JerinTJ-7/esp32-8x16-led-matrix-display/Images/led display pcb5.png

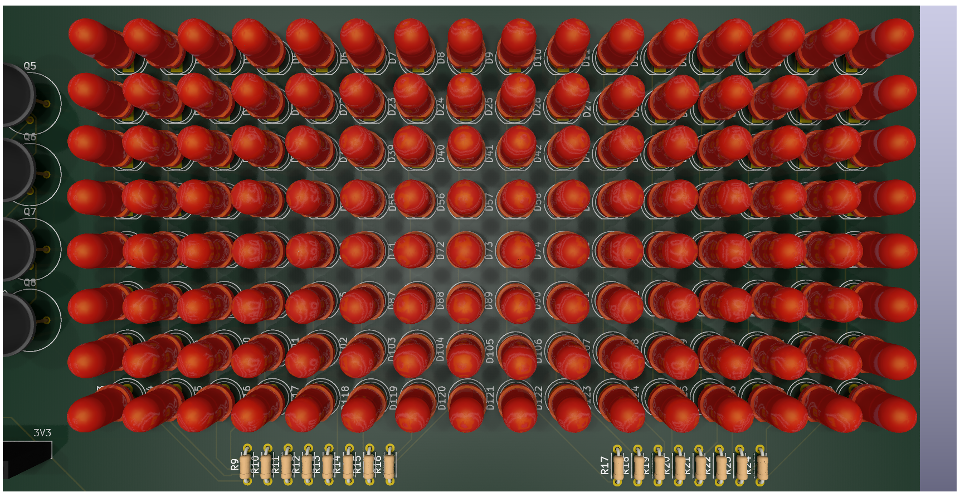
Images/led display pcb5.png
