JerinTJ-7/esp32-8x16-led-matrix-display/Images/led display pcb7.png

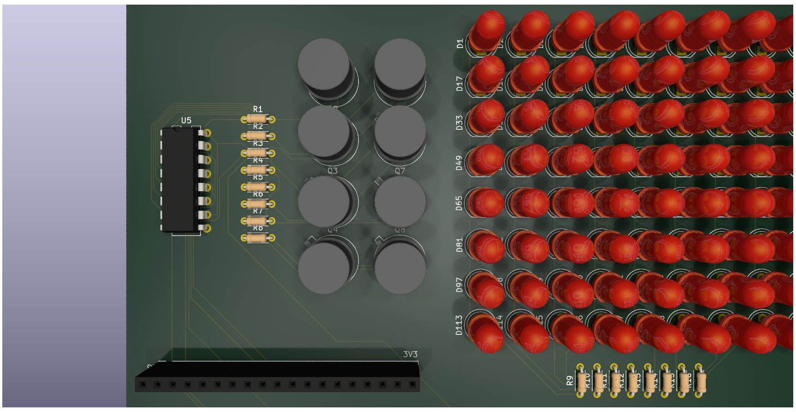
Images/led display pcb7.png
