JerinTJ-7/esp32-8x16-led-matrix-display/Images/PCB Layout.png

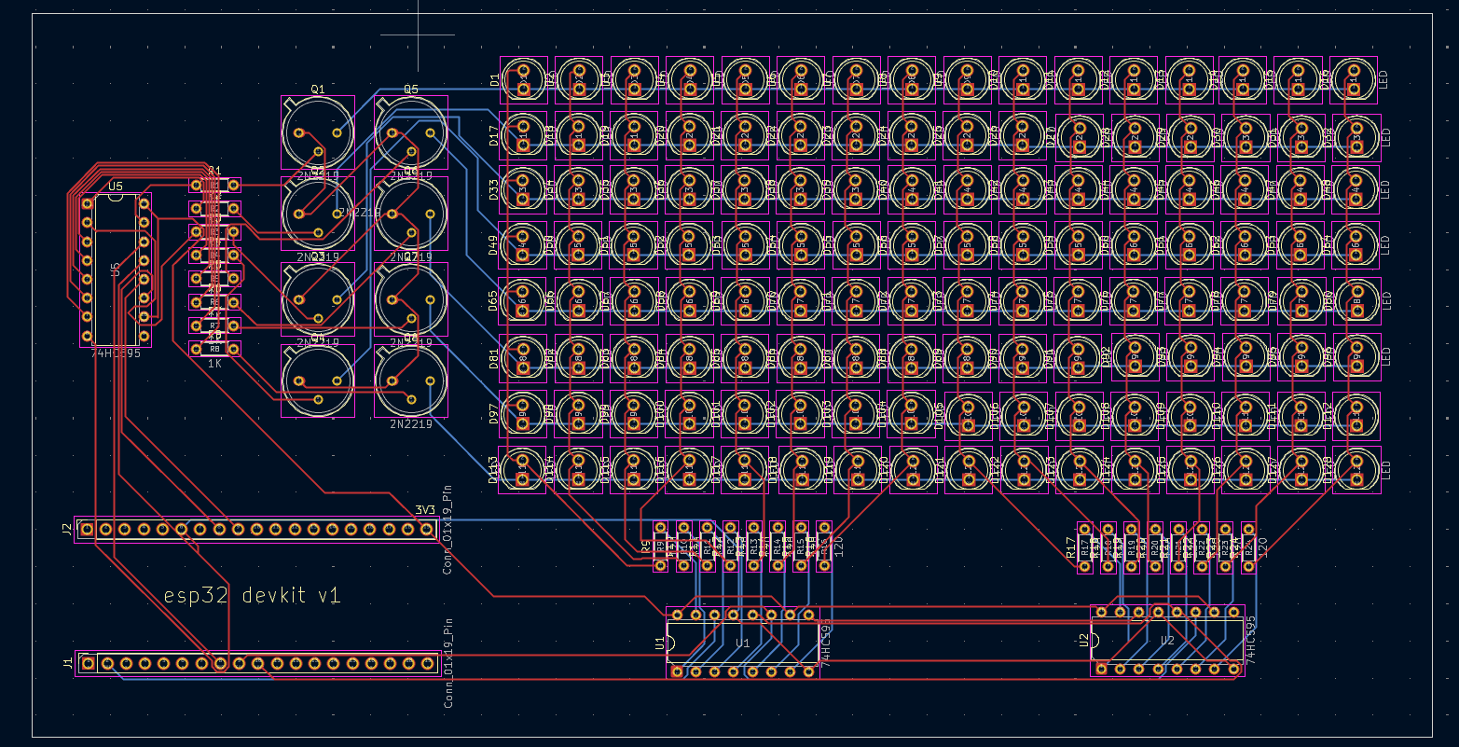
Images/PCB Layout.png
