JerinTJ-7/esp32-8x16-led-matrix-display/Images/schematic_row.png

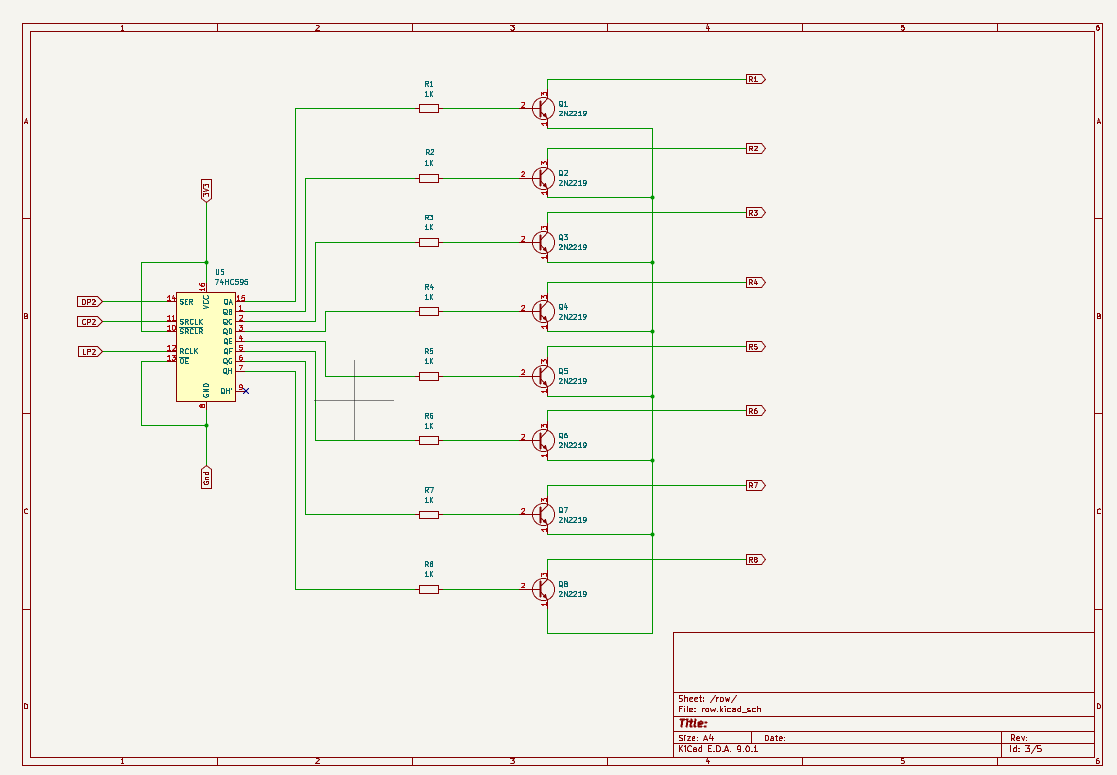
Images/schematic_row.png
