JerinTJ-7/esp32-8x16-led-matrix-display/Simulation/images/circuit.png

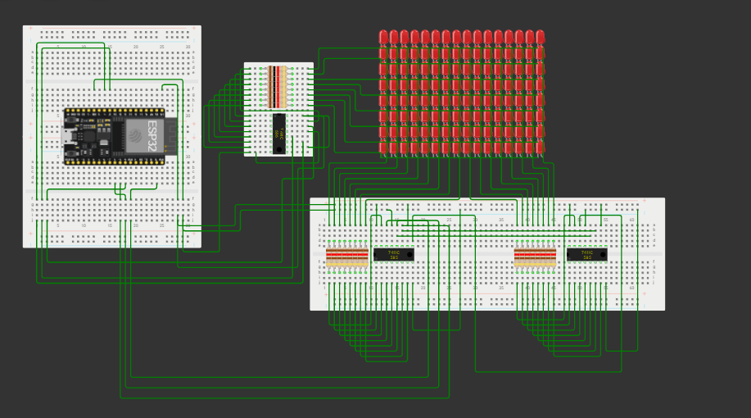
Simulation/images/circuit.png
